palette-system/nubkey_module/images/hall.png

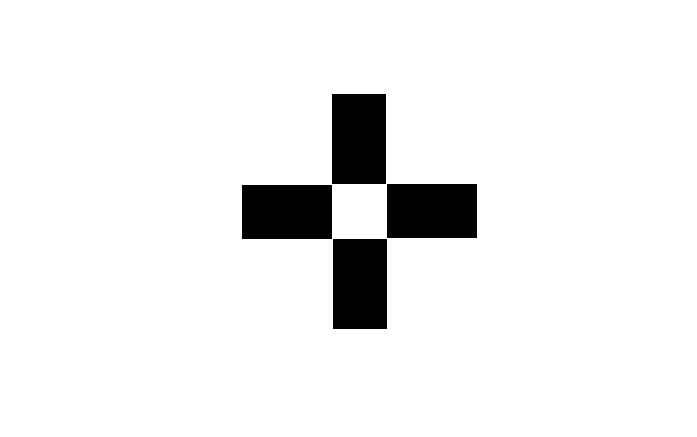
images/hall.png
