palette-system/nubkey_module/images/nubkey_danmen.png

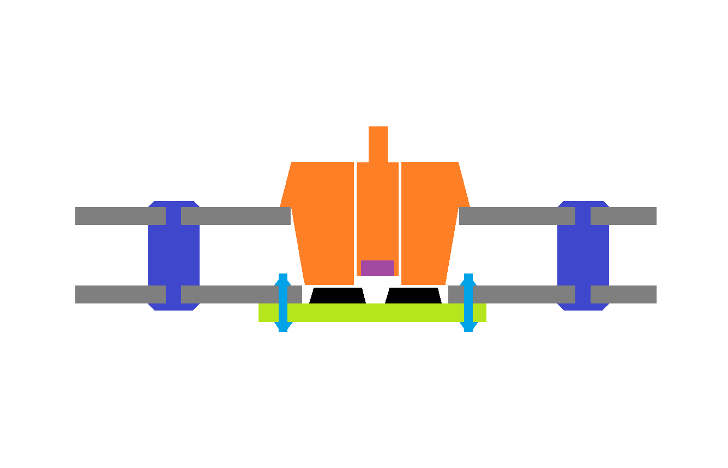
images/nubkey_danmen.png
