palette-system/nubkey_module/images/pcb_muki.png

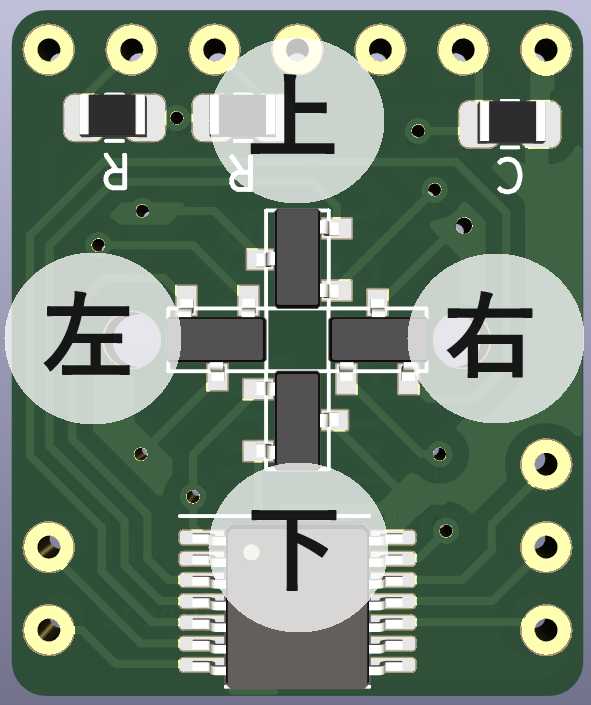
images/pcb_muki.png
